Miceuz/TV-B-Gone/pics/for web/IMG_8427.jpg

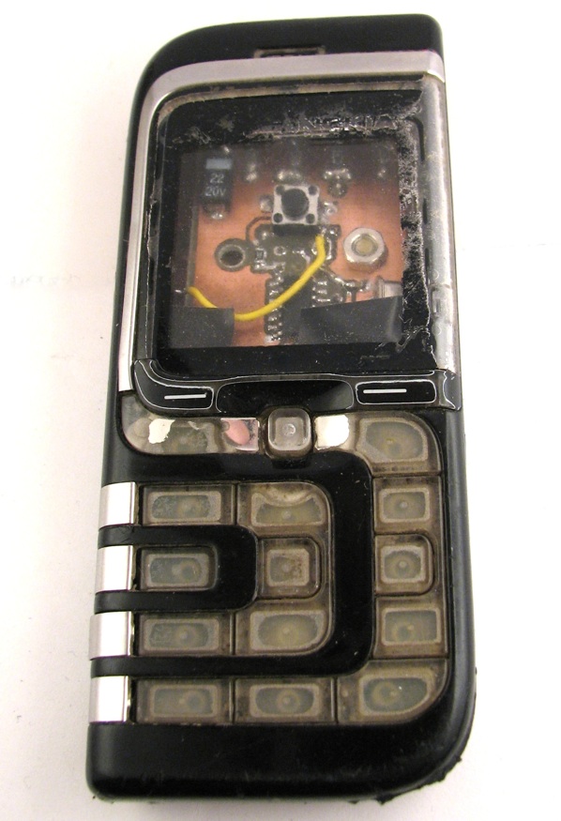
pics/for web/IMG_8427.jpg
