Miceuz/TV-B-Gone/pics/IMG_8427.JPG

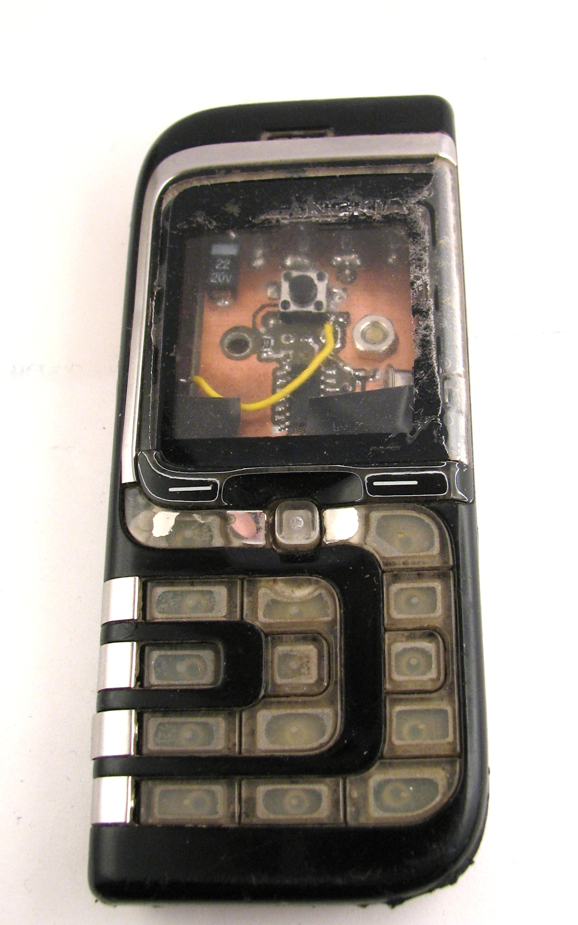
pics/IMG_8427.JPG
