Miceuz/TV-B-Gone/tvbgone-workshop/BK-92.jpg

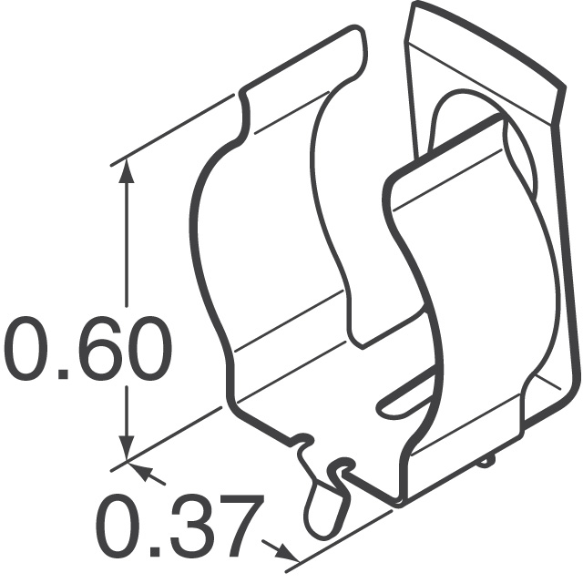
tvbgone-workshop/BK-92.jpg
