Miceuz/TV-B-Gone/tvbgone-workshop/tvbgone-workshop.png

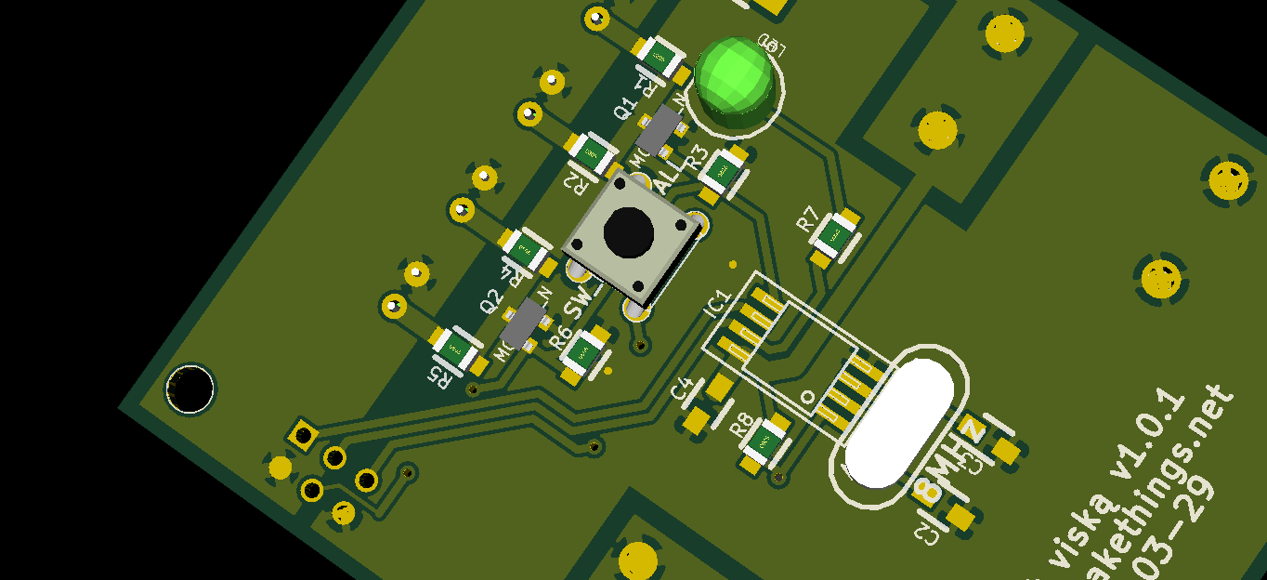
tvbgone-workshop/tvbgone-workshop.png
