Miceuz/TV-B-Gone/tvbgone-workshop/tvbgone-workshop.sch

## KiCad design tvbgone-workshop/tvbgone-workshop.sch (2014-03-29, an earlier design)

Schematic: tvbgone-workshop.sch

Parts:
BT1, BT2: BATTERY
C1: CAPAPOL
C2, C3: 22p
C4: 100n
CON1: AVR-ISP-6
D1, D2, D3, D4, D5: LED
IC1: ATTINY85-S; SO8-200
Q1, Q2: MOSFET_N
R1, R2, R3, R4, R5, R6, R8: 10k
R7: 330
SW1: SW_PUSH_SMALL
X1: 8MHz
